msx-solis/Omega_DC-DC_adaptor_1.5/documentacion/Omega_DC-DC_adaptor_1.6-f.jpg

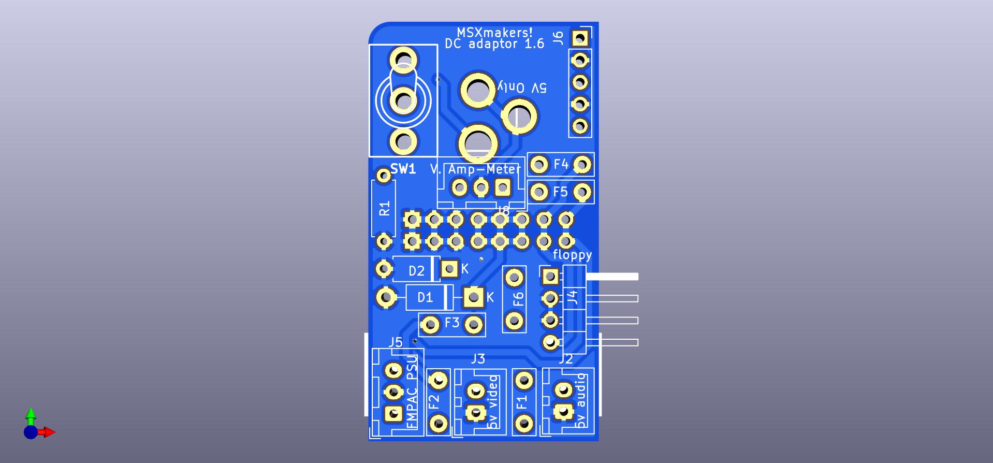
documentacion/Omega_DC-DC_adaptor_1.6-f.jpg
