msx-solis/Omega_DC-DC_adaptor_1.5/pictures/IMG_20210625_1243486.jpg

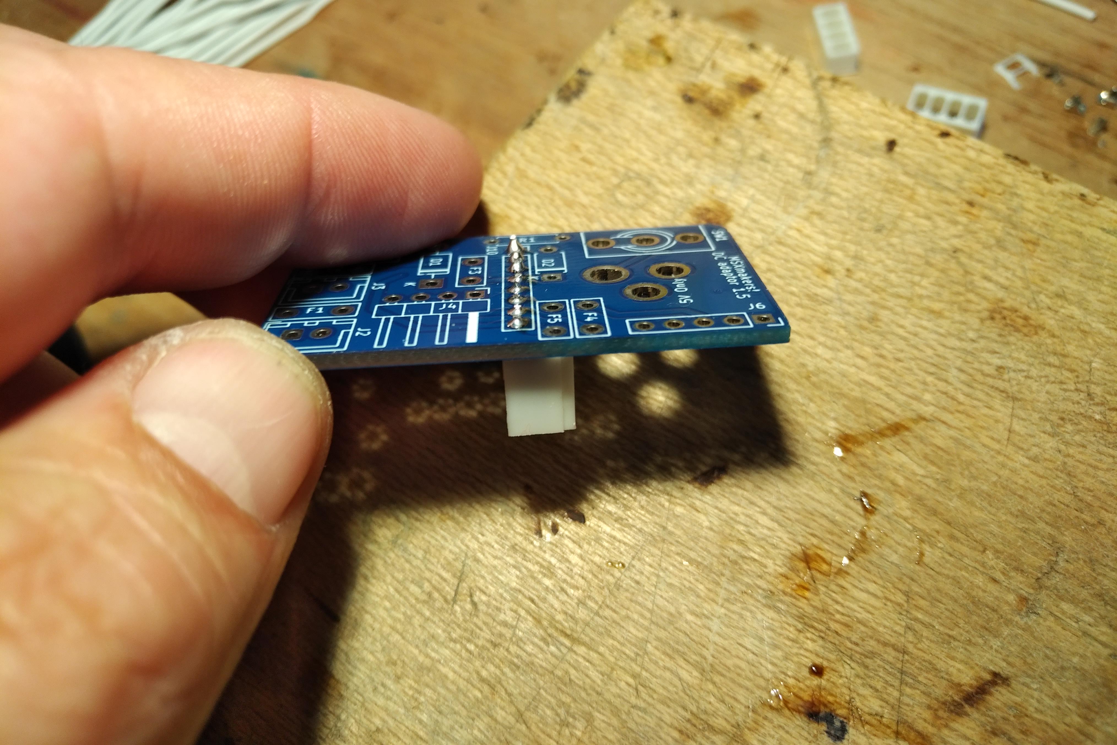
pictures/IMG_20210625_1243486.jpg
