msx-solis/Omega_DC-DC_adaptor_1.5/pictures/IMG_20210710_0220552.jpg

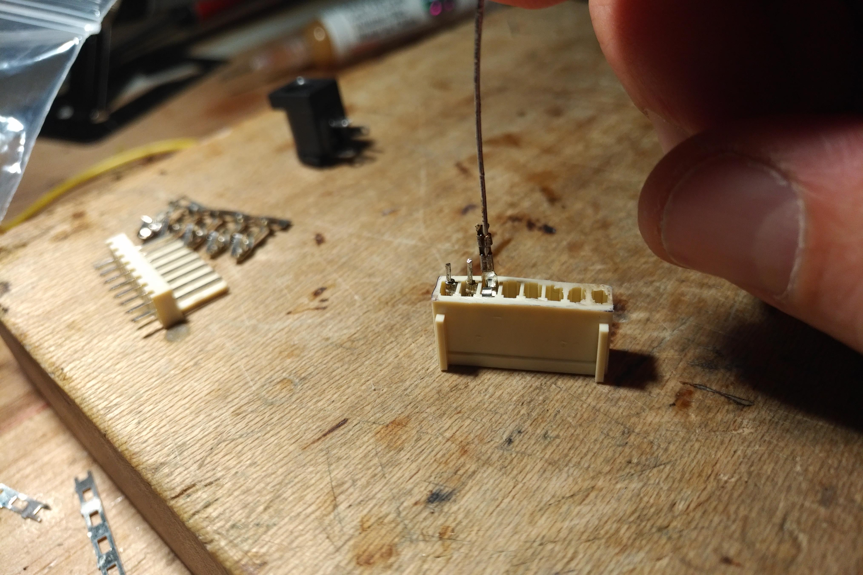
pictures/IMG_20210710_0220552.jpg
