msx-solis/Omega_DC-DC_adaptor_1.5/pictures/IMG_20210716_1044411.jpg

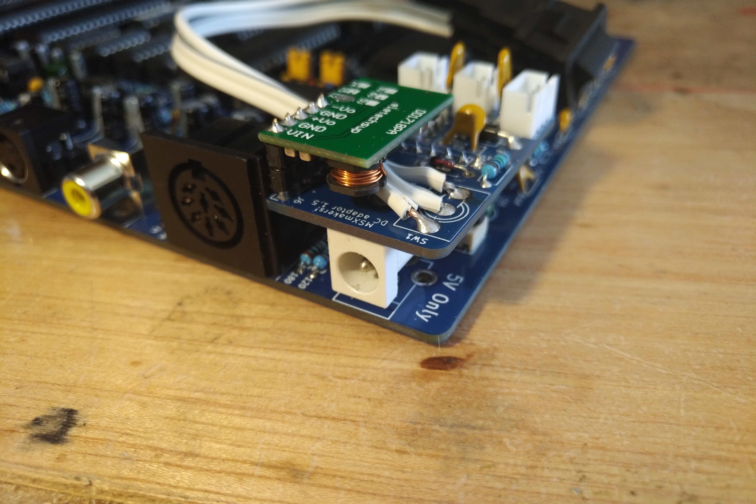
pictures/IMG_20210716_1044411.jpg
