msx-solis/Omega_DC-DC_adaptor_1.5/pictures/IMG_20210825_0936522.jpg

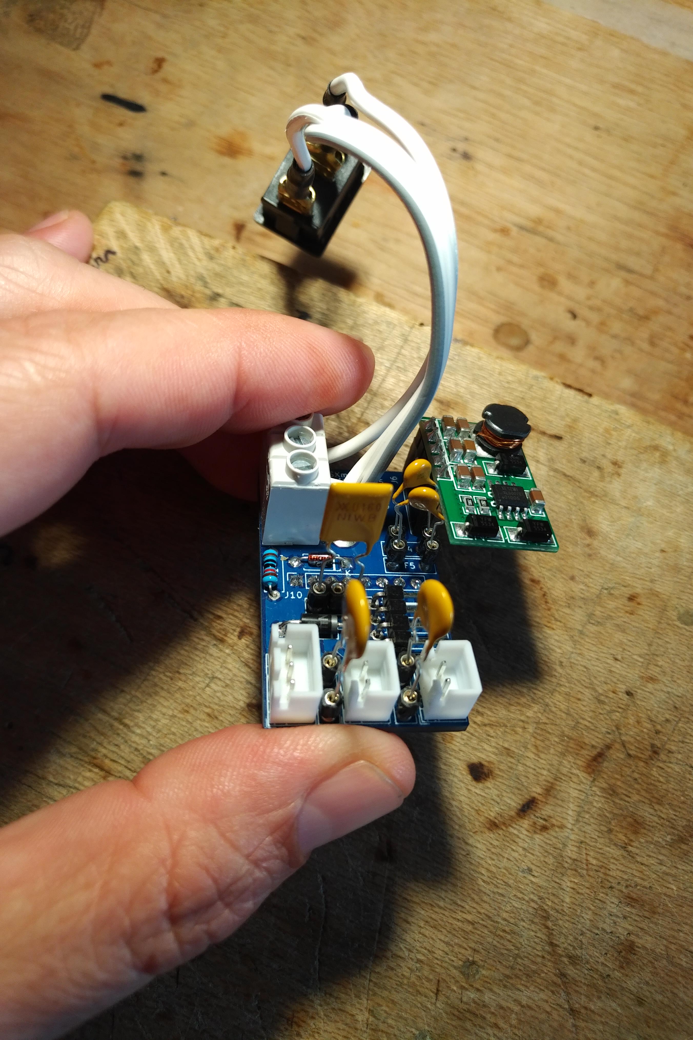
pictures/IMG_20210825_0936522.jpg
