msx-solis/Omega_DC-DC_adaptor_1.5/pictures/IMG_20211120_1221399.jpg

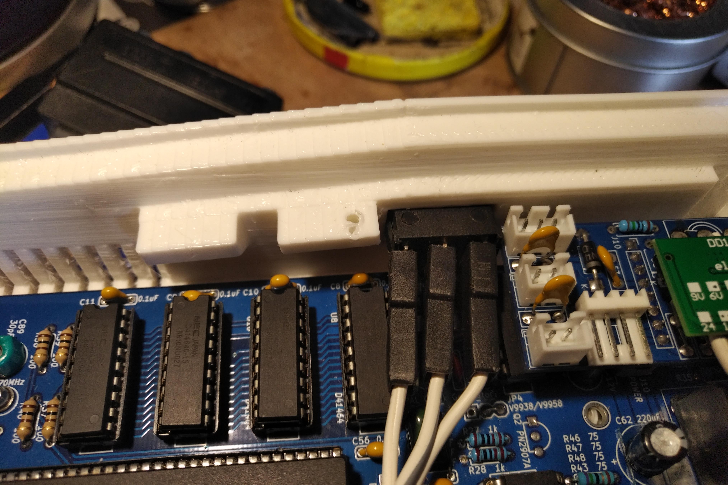
pictures/IMG_20211120_1221399.jpg
