msx-solis/Omega_DC-DC_adaptor_1.5/pictures/IMG_20211205_0153137.jpg

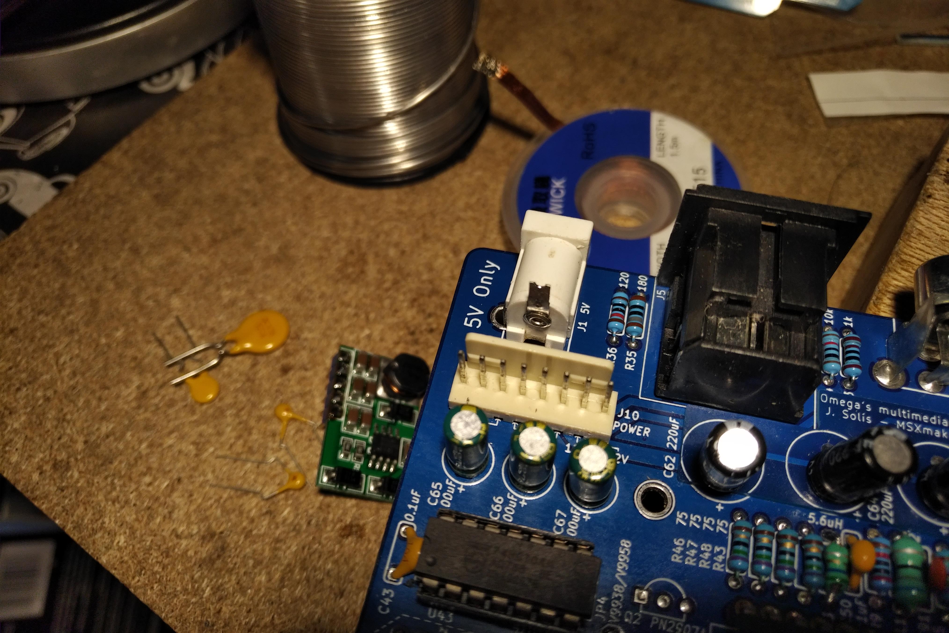
pictures/IMG_20211205_0153137.jpg
